pointhi/PointhiBoard/doc/images/circuit_full.png

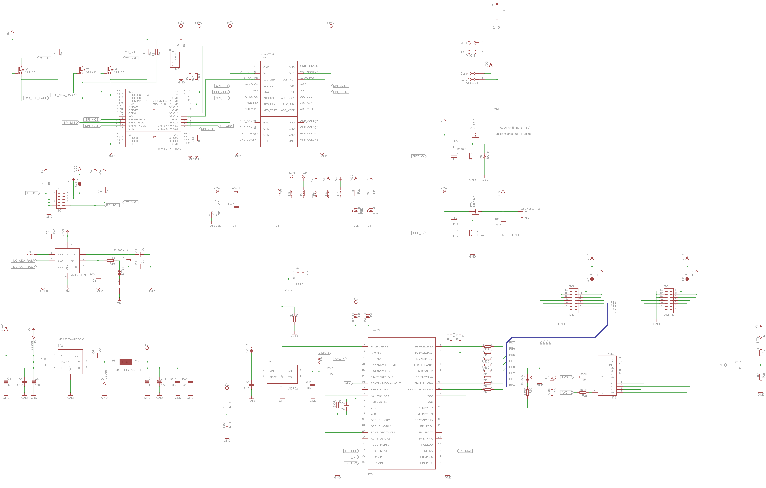
doc/images/circuit_full.png
