pointhi/PointhiBoard/firmware/PointhiBoard_fw.X/src/io.h

/**
 * @file io.h
 *
 * @author thomas
 *
 * @date 1. March 2014
 * @copyright GNU General Public License (GPL) 3.0
 */

#ifndef IO_H
#define	IO_H

inline void IoSetLedInfo(const unsigned char _ledMacro);
inline void IoSetLedStat(const unsigned char _ledMacro);

void IoGotoNextMacroBit();
void IoUpdateLedOutput();

void IoSetFet5v(const unsigned char _value);
void IoSetFetVcc(const unsigned char _value);

/** 
 * @brief Set which port is Input, and which is output
 *
 * @param _value 1... Input, 0... Output
 */
inline void IoSetPortBTris(const unsigned char _value);
inline unsigned char IoGetPortBTris();

inline void IoSetPortB(const unsigned char _value);
inline unsigned char IoGetPortB();

#endif	/* IO_H */
